dcasati/rc-xbox-controller/hardware/rc-xbox-controller.kicad_sch

## KiCad design hardware/rc-xbox-controller.kicad_sch (2026-04-07)

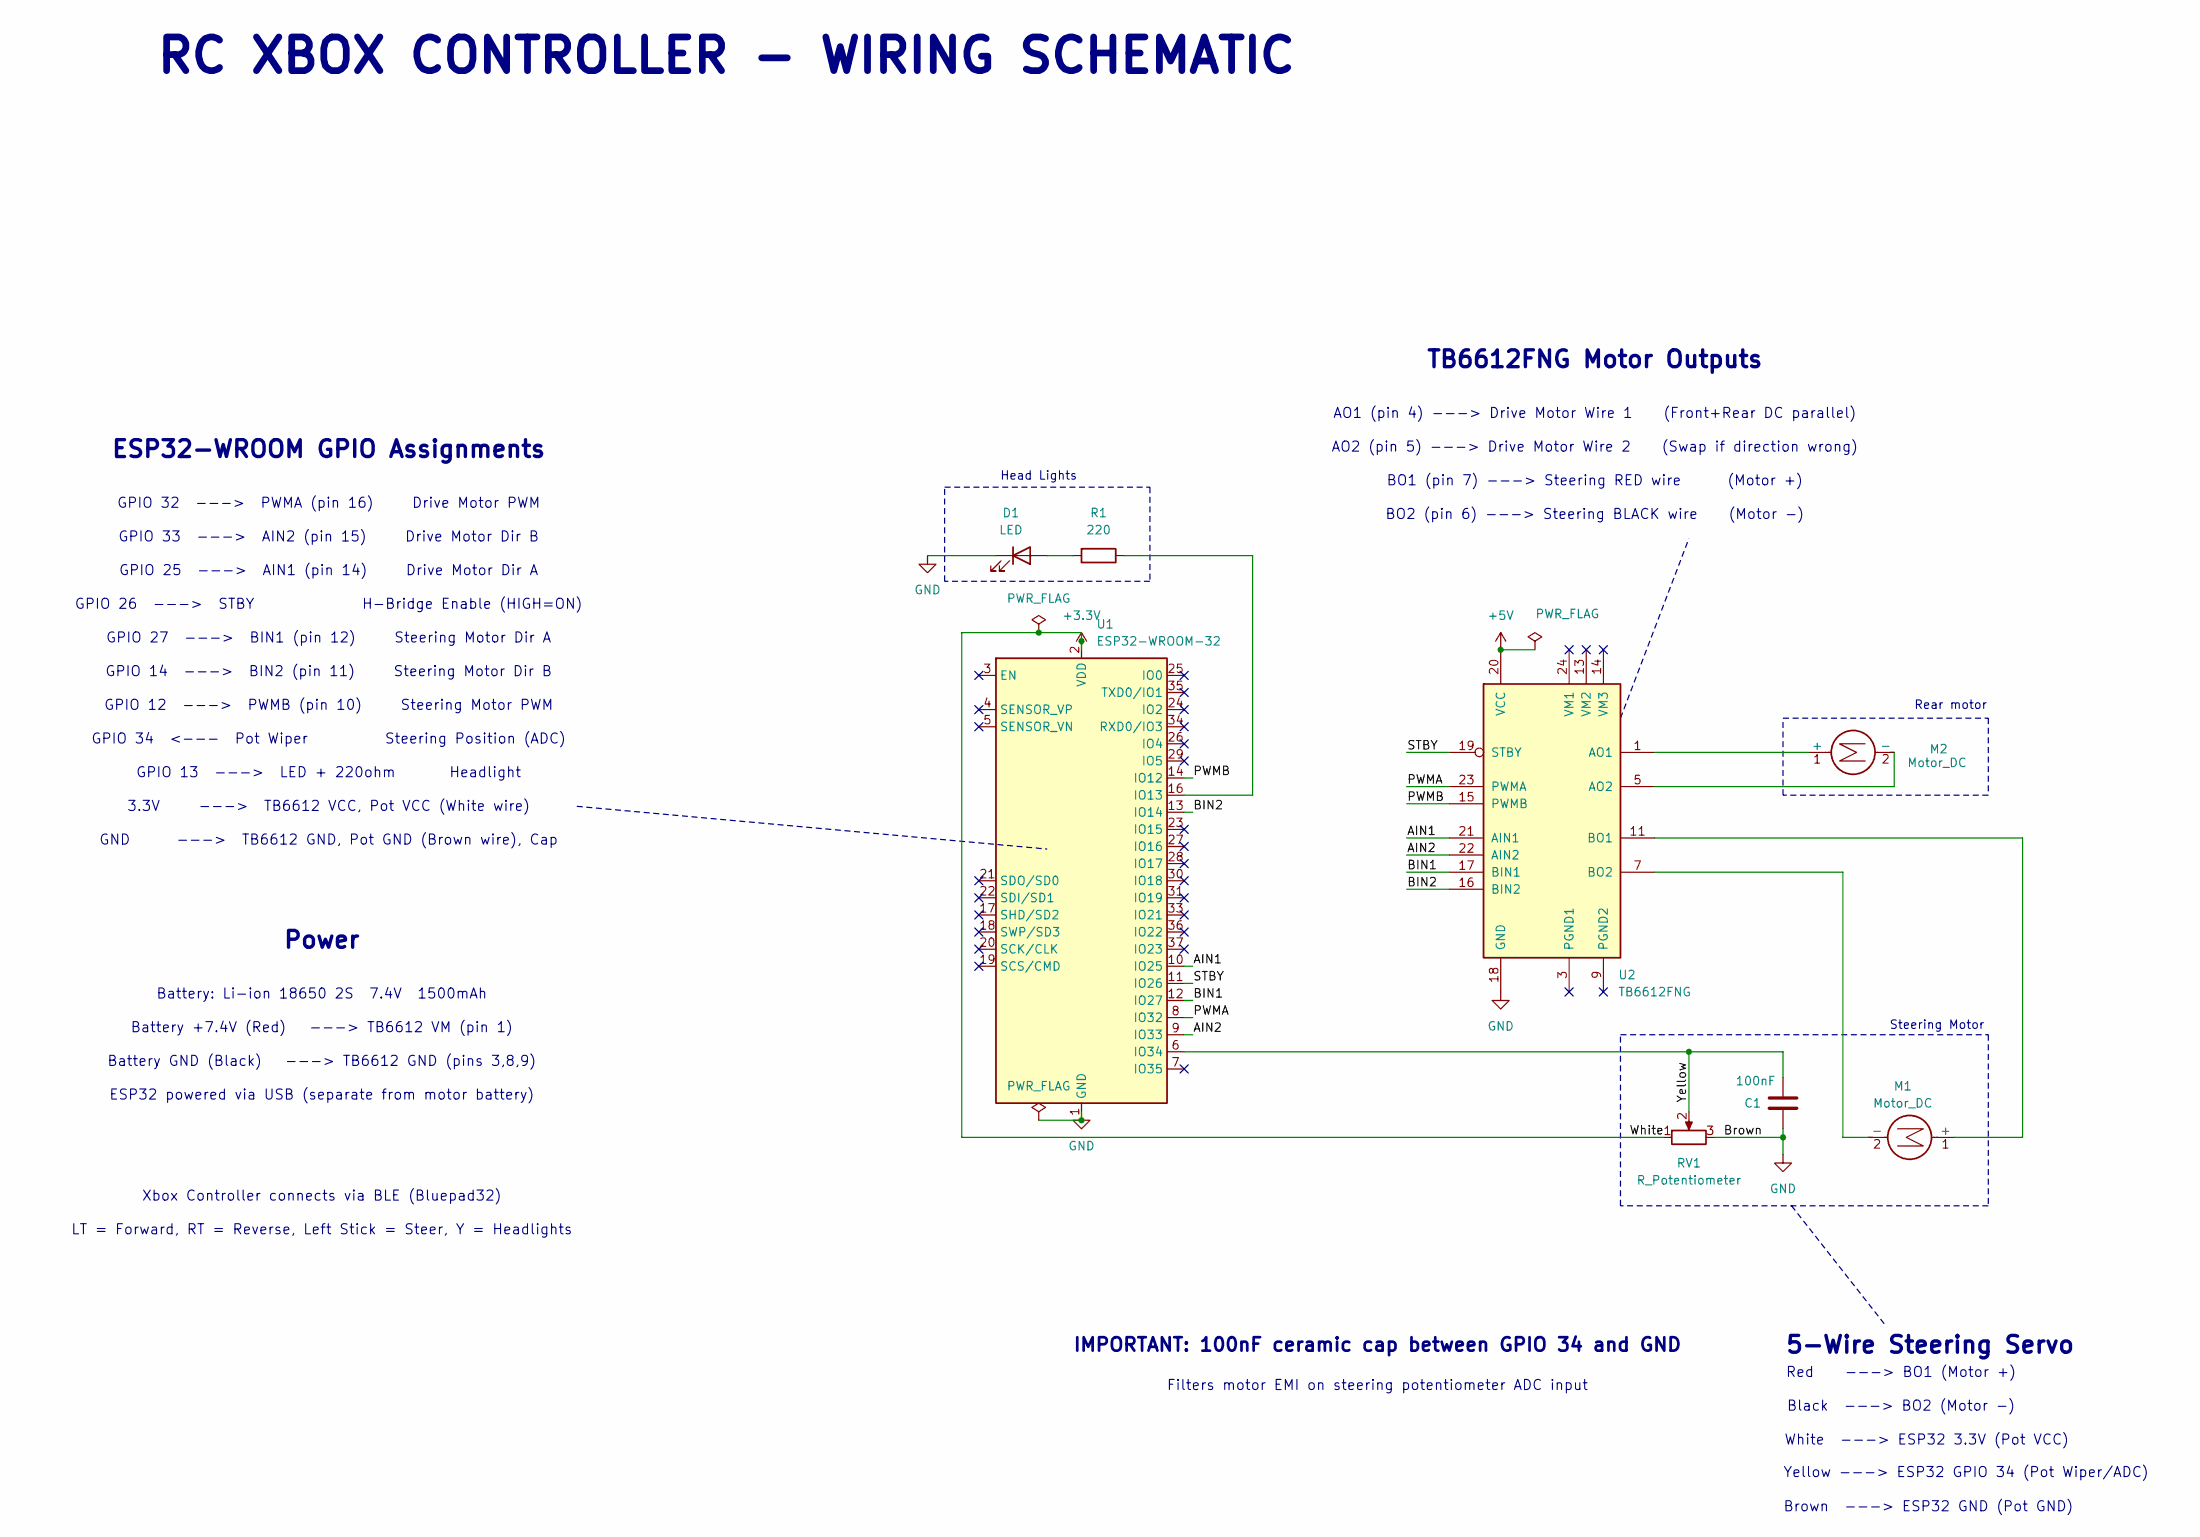
[picture p7: schematic rc-xbox-controller.kicad_sch]

Parts:
C1: 100nF
D1: LED
M1, M2: Motor_DC
R1: 220
RV1: R_Potentiometer
U1: ESP32-WROOM-32
U2: TB6612FNG; SSOP-24_5.3x8.2mm_P0.65mm

Connections:
+3.3V: RV1.1, U1.2 (VDD)
+5V: U2.20 (VCC)
AIN1: U1.10 (IO25), U2.21 (AIN1)
AIN2: U1.9 (IO33), U2.22 (AIN2)
BIN1: U1.12 (IO27), U2.17 (BIN1)
BIN2: U1.13 (IO14), U2.16 (BIN2)
GND: C1.2, D1.1 (K), RV1.3, U1.1 (GND), U1.15 (GND), U1.38 (GND), U1.39 (GND), U2.18 (GND)
unnamed: D1.2 (A), R1.2
unnamed: M1.1 (+), U2.11 (BO1), U2.12 (BO1)
unnamed: M1.2 (-), U2.7 (BO2), U2.8 (BO2)
unnamed: M2.1 (+), U2.1 (AO1), U2.2 (AO1)
unnamed: M2.2 (-), U2.5 (AO2), U2.6 (AO2)
unnamed: R1.1, U1.16 (IO13)
unnamed: U2.3 (PGND1), U2.4 (PGND1)
unnamed: U2.9 (PGND2), U2.10 (PGND2)
PWMA: U1.8 (IO32), U2.23 (PWMA)
PWMB: U1.14 (IO12), U2.15 (PWMB)
STBY: U1.11 (IO26), U2.19 (STBY)
Yellow: C1.1, RV1.2, U1.6 (IO34)

Notes on the sheet:
BO1 (pin 7) ---> Steering RED wire (Motor +)
GPIO 26 ---> STBY H-Bridge Enable (HIGH=ON)
RC XBOX CONTROLLER - WIRING SCHEMATIC
ESP32 powered via USB (separate from motor battery)
Xbox Controller connects via BLE (Bluepad32)
Black ---> BO2 (Motor -)
GPIO 25 ---> AIN1 (pin 14) Drive Motor Dir A
IMPORTANT: 100nF ceramic cap between GPIO 34 and GND
Filters motor EMI on steering potentiometer ADC input
Brown ---> ESP32 GND (Pot GND)
GPIO 12 ---> PWMB (pin 10) Steering Motor PWM
BO2 (pin 6) ---> Steering BLACK wire (Motor -)
Rear motor
Head Lights
TB6612FNG Motor Outputs
Yellow ---> ESP32 GPIO 34 (Pot Wiper/ADC)
Battery GND (Black) ---> TB6612 GND (pins 3,8,9)
5-Wire Steering Servo
AO1 (pin 4) ---> Drive Motor Wire 1 (Front+Rear DC parallel)
Steering Motor
GND ---> TB6612 GND, Pot GND (Brown wire), Cap
ESP32-WROOM GPIO Assignments
GPIO 27 ---> BIN1 (pin 12) Steering Motor Dir A
GPIO 13 ---> LED + 220ohm Headlight
Power
Battery +7.4V (Red) ---> TB6612 VM (pin 1)
White ---> ESP32 3.3V (Pot VCC)
3.3V ---> TB6612 VCC, Pot VCC (White wire)
Red ---> BO1 (Motor +)
GPIO 33 ---> AIN2 (pin 15) Drive Motor Dir B
Battery: Li-ion 18650 2S 7.4V 1500mAh
LT = Forward, RT = Reverse, Left Stick = Steer, Y = Headlights
GPIO 32 ---> PWMA (pin 16) Drive Motor PWM
GPIO 34 <--- Pot Wiper Steering Position (ADC)
GPIO 14 ---> BIN2 (pin 11) Steering Motor Dir B
AO2 (pin 5) ---> Drive Motor Wire 2 (Swap if direction wrong)
