dcasati/rc-xbox-controller/main/wifi.c

// SPDX-License-Identifier: MIT
// RC Xbox Controller — Wi-Fi Station Connection

#include "wifi.h"

#include <string.h>

#include <esp_event.h>
#include <esp_log.h>
#include <esp_netif.h>
#include <esp_wifi.h>
#include <freertos/FreeRTOS.h>
#include <freertos/event_groups.h>

#include "sdkconfig.h"

static const char* TAG = "wifi";

#define WIFI_CONNECTED_BIT BIT0
#define WIFI_FAIL_BIT      BIT1
#define WIFI_MAX_RETRY     5

static EventGroupHandle_t s_wifi_event_group;
static int s_retry_num = 0;

static void event_handler(void* arg, esp_event_base_t event_base,
                           int32_t event_id, void* event_data) {
    if (event_base == WIFI_EVENT && event_id == WIFI_EVENT_STA_START) {
        esp_wifi_connect();
    } else if (event_base == WIFI_EVENT && event_id == WIFI_EVENT_STA_DISCONNECTED) {
        if (s_retry_num < WIFI_MAX_RETRY) {
            esp_wifi_connect();
            s_retry_num++;
            ESP_LOGW(TAG, "Retrying connection (%d/%d)", s_retry_num, WIFI_MAX_RETRY);
        } else {
            xEventGroupSetBits(s_wifi_event_group, WIFI_FAIL_BIT);
            ESP_LOGE(TAG, "Failed to connect after %d retries", WIFI_MAX_RETRY);
        }
    } else if (event_base == IP_EVENT && event_id == IP_EVENT_STA_GOT_IP) {
        ip_event_got_ip_t* event = (ip_event_got_ip_t*)event_data;
        ESP_LOGI(TAG, "Connected! IP: " IPSTR, IP2STR(&event->ip_info.ip));
        s_retry_num = 0;
        xEventGroupSetBits(s_wifi_event_group, WIFI_CONNECTED_BIT);
    }
}

esp_err_t wifi_init_sta(void) {
    s_wifi_event_group = xEventGroupCreate();

    ESP_ERROR_CHECK(esp_netif_init());
    ESP_ERROR_CHECK(esp_event_loop_create_default());
    esp_netif_create_default_wifi_sta();

    wifi_init_config_t cfg = WIFI_INIT_CONFIG_DEFAULT();
    ESP_ERROR_CHECK(esp_wifi_init(&cfg));

    esp_event_handler_instance_t instance_any_id;
    esp_event_handler_instance_t instance_got_ip;
    ESP_ERROR_CHECK(esp_event_handler_instance_register(WIFI_EVENT,
                                                         ESP_EVENT_ANY_ID,
                                                         &event_handler,
                                                         NULL,
                                                         &instance_any_id));
    ESP_ERROR_CHECK(esp_event_handler_instance_register(IP_EVENT,
                                                         IP_EVENT_STA_GOT_IP,
                                                         &event_handler,
                                                         NULL,
                                                         &instance_got_ip));

    wifi_config_t wifi_config = {
        .sta = {
            .ssid = CONFIG_RC_WIFI_SSID,
            .password = CONFIG_RC_WIFI_PASSWORD,
            .threshold.authmode = WIFI_AUTH_WPA2_PSK,
        },
    };
    ESP_ERROR_CHECK(esp_wifi_set_mode(WIFI_MODE_STA));
    ESP_ERROR_CHECK(esp_wifi_set_config(WIFI_IF_STA, &wifi_config));
    ESP_ERROR_CHECK(esp_wifi_start());

    ESP_LOGI(TAG, "Connecting to SSID: %s", CONFIG_RC_WIFI_SSID);

    // Wait until connected or failed
    EventBits_t bits = xEventGroupWaitBits(s_wifi_event_group,
                                            WIFI_CONNECTED_BIT | WIFI_FAIL_BIT,
                                            pdFALSE, pdFALSE, portMAX_DELAY);

    if (bits & WIFI_CONNECTED_BIT) {
        ESP_LOGI(TAG, "Wi-Fi connected to %s", CONFIG_RC_WIFI_SSID);
        return ESP_OK;
    }

    ESP_LOGE(TAG, "Wi-Fi connection failed");
    return ESP_FAIL;
}
