dcasati/rc-xbox-controller/main/my_platform.h

// SPDX-License-Identifier: MIT
// RC Xbox Controller — Bluepad32 Custom Platform

#ifndef MY_PLATFORM_H
#define MY_PLATFORM_H

#include <uni.h>

struct uni_platform* get_my_platform(void);

#endif // MY_PLATFORM_H
